samiulbasher/ST-Link-JTAG_to_SWD/utility/nucleo_stlink.png

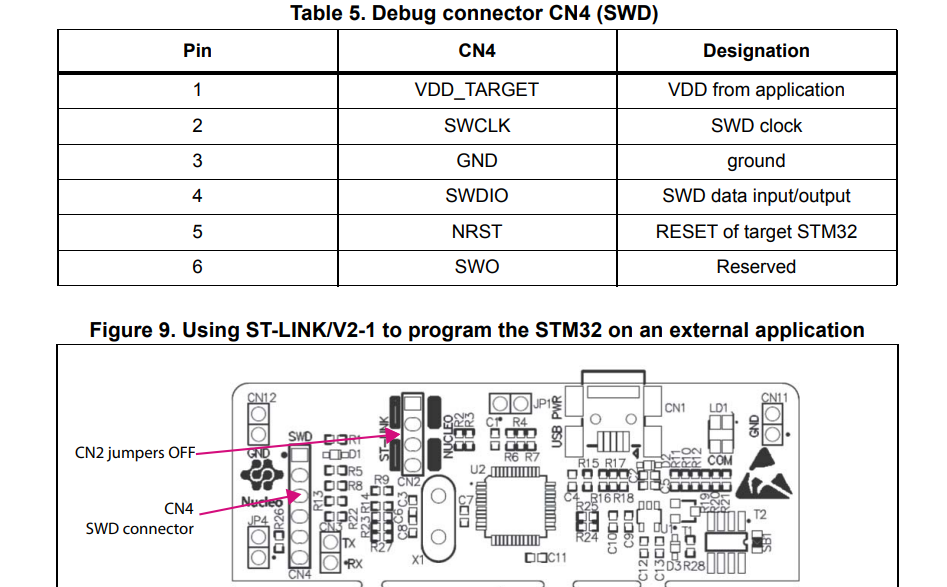
utility/nucleo_stlink.png
